sthivaios/northreach_1/enclosure/v2/exports/northreach_1_v2_RectangleButton.stl

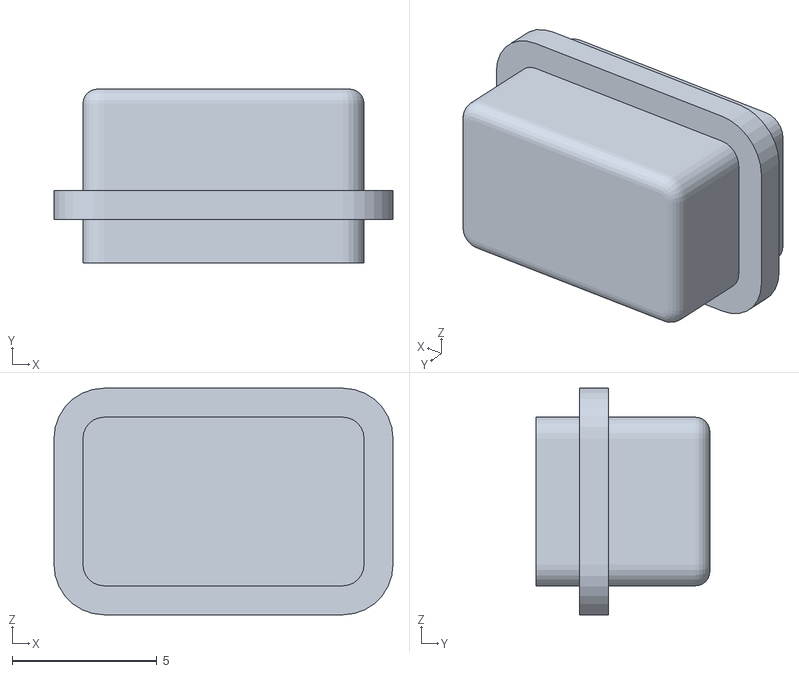
[picture p15: CAD file, 2026-01-06, an earlier design]
enclosure/v2/exports/northreach_1_v2_RectangleButton.stl
11.7 x 6.00 x 7.82
